Megazoids-Hut/CrokPocket/images/c2.jpg

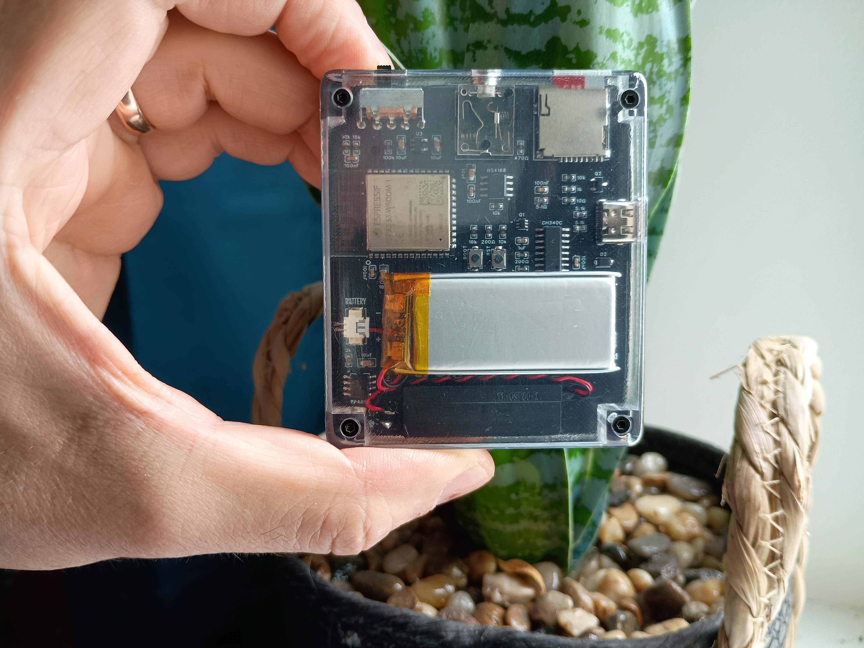
images/c2.jpg
