Megazoids-Hut/CrokPocket/images/c3.png

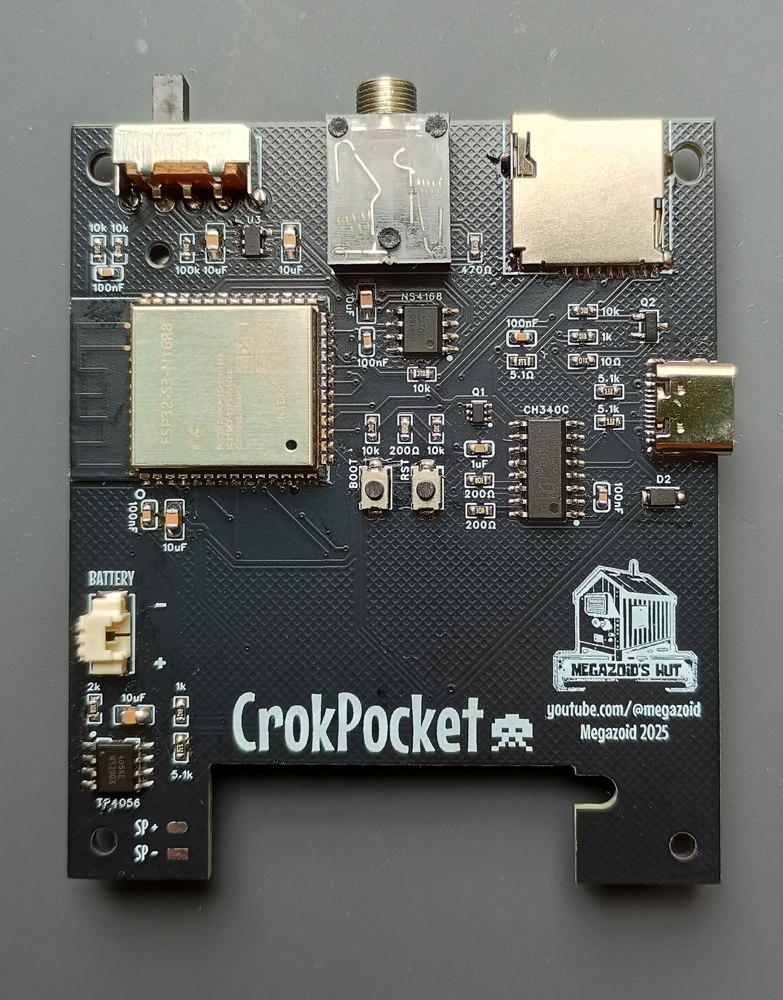
images/c3.png
